DigiFennek/TransputerBox/MCUXpresso/transputerBox_WinUSB_cm4/source/libusbdev_desc.c

/*
 * @brief USB Band Width and WCID example descriptors.
 *
 * @note
 * Copyright(C) NXP Semiconductors, 2013
 * All rights reserved.
 *
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
 * @par
 * Permission to use, copy, modify, and distribute this software and its
 * documentation is hereby granted, under NXP Semiconductors' and its
 * licensor's relevant copyrights in the software, without fee, provided that it
 * is used in conjunction with NXP Semiconductors microcontrollers.  This
 * copyright, permission, and disclaimer notice must appear in all copies of
 * this code.
 */

#include "app_usbd_cfg.h"
#include "usbd_rom_api.h"

/*****************************************************************************
 * Private types/enumerations/variables
 ****************************************************************************/

/*****************************************************************************
 * Public types/enumerations/variables
 ****************************************************************************/

/**
 * USB Standard Device Descriptor
 */
ALIGN(4) const uint8_t USB_DeviceDescriptor[] = {
	USB_DEVICE_DESC_SIZE,				/* bLength */
	USB_DEVICE_DESCRIPTOR_TYPE,			/* bDescriptorType */
	WBVAL(0x0200),						/* bcdUSB: 2.00 */
	0x00,								/* bDeviceClass */
	0x00,								/* bDeviceSubClass */
	0x00,								/* bDeviceProtocol */
	USB_MAX_PACKET0,					/* bMaxPacketSize0 */
	WBVAL(0x1FC9),						/* idVendor */
	WBVAL(LUSB_PID),					/* idProduct */
	WBVAL(0x0100),						/* bcdDevice: 1.00 */
	0x01,								/* iManufacturer */
	0x02,								/* iProduct */
	0x03,								/* iSerialNumber */
	0x01								/* bNumConfigurations */
};

/**
 * USB FSConfiguration Descriptor
 * All Descriptors (Configuration, Interface, Endpoint, Class, Vendor)
 */
ALIGNED(4) uint8_t USB_FsConfigDescriptor[] = {
	/* Configuration 1 */
	USB_CONFIGURATION_DESC_SIZE,		/* bLength */
	USB_CONFIGURATION_DESCRIPTOR_TYPE,	/* bDescriptorType */
	WBVAL(							/* wTotalLength */
		USB_CONFIGURATION_DESC_SIZE +
		USB_INTERFACE_DESC_SIZE     +
		LUSB_NUM_OF_EP * USB_ENDPOINT_DESC_SIZE
		),
	0x01,							/* bNumInterfaces */
	0x01,							/* bConfigurationValue */
	0x00,							/* iConfiguration */
	USB_CONFIG_SELF_POWERED,		/* bmAttributes */
	USB_CONFIG_POWER_MA(100),		/* bMaxPower */
	/* Interface 0, Alternate Setting 0, Custom Class */
	USB_INTERFACE_DESC_SIZE,		/* bLength */
	USB_INTERFACE_DESCRIPTOR_TYPE,	/* bDescriptorType */
	0x00,							/* bInterfaceNumber */
	0x00,							/* bAlternateSetting */
	LUSB_NUM_OF_EP,					/* bNumEndpoints */
	0xFF,							/* bInterfaceClass */
	0xF0,							/* bInterfaceSubClass */
	0x00,							/* bInterfaceProtocol */
	0x04,							/* iInterface */
	/* Bulk Out Endpoint */
	USB_ENDPOINT_DESC_SIZE,			/* bLength */
	USB_ENDPOINT_DESCRIPTOR_TYPE,	/* bDescriptorType */
	LUSB_OUT_EP,					/* bEndpointAddress */
	USB_ENDPOINT_TYPE_BULK,			/* bmAttributes */
	WBVAL(USB_FS_MAX_BULK_PACKET),	/* wMaxPacketSize */
	0,								/* bInterval */
	/* Bulk In Endpoint */
	USB_ENDPOINT_DESC_SIZE,			/* bLength */
	USB_ENDPOINT_DESCRIPTOR_TYPE,	/* bDescriptorType */
	LUSB_IN_EP,						/* bEndpointAddress */
	USB_ENDPOINT_TYPE_BULK,			/* bmAttributes */
	WBVAL(USB_FS_MAX_BULK_PACKET),	/* wMaxPacketSize */
	0,								/* bInterval */
	/* INT Out Endpoint */
	USB_ENDPOINT_DESC_SIZE,			/* bLength */
	USB_ENDPOINT_DESCRIPTOR_TYPE,	/* bDescriptorType */
	LUSB_INTR_OUT_EP,				/* bEndpointAddress */
	USB_ENDPOINT_TYPE_INTERRUPT,	/* bmAttributes */
	WBVAL(sizeof(uint32_t)),        /* wMaxPacketSize */
	0,	     						/* bInterval: 8 ms */
	/* INT In Endpoint */
	USB_ENDPOINT_DESC_SIZE,			/* bLength */
	USB_ENDPOINT_DESCRIPTOR_TYPE,	/* bDescriptorType */
	LUSB_INTR_IN_EP,				/* bEndpointAddress */
	USB_ENDPOINT_TYPE_INTERRUPT,	/* bmAttributes */
	WBVAL(sizeof(uint32_t)),		/* wMaxPacketSize */
	0x8,							/* bInterval: 8 ms */
	/* Terminator */
	0								/* bLength */
};

/**
 * USB String Descriptor (optional)
 */
const uint8_t USB_StringDescriptor[] = {
	/* Index 0x00: LANGID Codes */
	0x04,							/* bLength */
	USB_STRING_DESCRIPTOR_TYPE,		/* bDescriptorType */
	WBVAL(0x0409),					/* wLANGID  0x0409 = US English*/
	/* Index 0x01: Manufacturer */
	(10 * 2 + 2),					/* bLength (18 Char + Type + length) */
	USB_STRING_DESCRIPTOR_TYPE,		/* bDescriptorType */
	'D', 0,
	'i', 0,
	'g', 0,
	'i', 0,
	'F', 0,
	'e', 0,
	'n', 0,
	'n', 0,
	'e', 0,
	'k', 0,
	/* Index 0x02: Product */
	(27 * 2 + 2),					/* bLength (15 Char + Type + length) */
	USB_STRING_DESCRIPTOR_TYPE,		/* bDescriptorType */
	'T', 0,
	'r', 0,
	'a', 0,
	'n', 0,
	's', 0,
	'p', 0,
	'u', 0,
	't', 0,
	'e', 0,
	'r', 0,
	'B', 0,
	'o', 0,
	'x', 0,
	' ', 0,
	'U', 0,
	'S', 0,
	'B', 0,
	' ', 0,
	'I', 0,
	'n', 0,
	't', 0,
	'e', 0,
	'r', 0,
	'f', 0,
	'a', 0,
	'c', 0,
	'e', 0,
	/* Index 0x03: Serial Number */
	(13 * 2 + 2),					/* bLength (13 Char + Type + length) */
	USB_STRING_DESCRIPTOR_TYPE,		/* bDescriptorType */
	'A', 0,
	'B', 0,
	'C', 0,
	'D', 0,
	'1', 0,
	'2', 0,
	'3', 0,
	'4', 0,
	'5', 0,
	'6', 0,
	'7', 0,
	'8', 0,
	'9', 0,
	/* Index 0x04: Interface 0, Alternate Setting 0 */
	(6 * 2 + 2),					/* bLength (6 Char + Type + length) */
	USB_STRING_DESCRIPTOR_TYPE,		/* bDescriptorType */
	'S', 0,
	't', 0,
	'r', 0,
	'e', 0,
	'a', 0,
	'm', 0,
};

/* WCID USB: Microsoft String Descriptor */
ALIGNED(4) const uint8_t WCID_String_Descriptor[] = {
	(8 * 2 + 2),					/* bLength (8 Char + Type + length) */
	USB_STRING_DESCRIPTOR_TYPE,		/* bDescriptorType */
	'M', 0,
	'S', 0,
	'F', 0,
	'T', 0,
	'1', 0,
	'0', 0,
	'0', 0,
	LUSB_PID, 0,
};

/* WCID USB: Microsoft Compatible ID Feature Descriptor */
ALIGNED(4) const uint8_t WCID_CompatID_Descriptor[] = {
	0x28, 0x00, 0x00, 0x00,						/* Length 40 bytes */
	0x00, 0x01,									/* Version */
	0x04, 0x00,									/* Compatibility ID Descriptor index  */
	0x01,										/* Number of sections */
	0x00, 0x00, 0x00, 0x00,
	0x00, 0x00, 0x00,							/* Reserved: 7 bytes */
	0x00,										/* Interface Number */
	0x01,										/* Reserved */
	'W', 'I', 'N', 'U', 'S', 'B', 0x00, 0x00,	/* Compatible ID: 8 bytes ASCII */
	0x00, 0x00, 0x00, 0x00,
	0x00, 0x00, 0x00, 0x00,						/* Sub-Compatible ID: 8 bytes ASCII*/
	0x00, 0x00, 0x00, 0x00,
	0x00, 0x00,									/* Reserved: 6 bytes */
};

/* WCID USB: Microsoft Extended Properties Feature Descriptor */
/* https://github.com/pbatard/libwdi/wiki/WCID-Devices#What_is_WCID */
ALIGNED(4) const uint8_t WCID_Properties_Descriptor[] = {
    0x8E, 0x00, 0x00, 0x00, 					/* Length 142 Bytes */
    0x00, 0x01,            						/* Version */
    0x05, 0x00,  	   							/* Descriptor index */
    0x01, 0x00,            						/* Number of sections */
    0x84, 0x00, 0x00, 0x00, 					/* Size of the property section (132 bytes) */
    0x01, 0x00, 0x00, 0x00,						/* Property data type */
    0x28, 0x00,    	   							/* Property name length (40 bytes) */
    'D', 0,
    'e', 0,
    'v', 0,
    'i', 0,
    'c', 0,
    'e', 0,
    'I', 0,
    'n', 0,
    't', 0,
    'e', 0,
    'r', 0,
    'f', 0,
    'a', 0,
    'c', 0,
    'e', 0,
    'G', 0,
    'U', 0,
    'I', 0,
    'D', 0,
    0x00, 0x00,            						/* NUL-terminated */
    0x4e, 0x00, 0x00, 0x00, 					/* Property data length (78 bytes) {60833b09-7fde-4410-afd1-541efdf36d8a} */
    '{', 0,
    '6', 0,
    '0', 0,
    '8', 0,
    '3', 0,
    '3', 0,
    'b', 0,
    '0', 0,
    '9', 0,
    '-', 0,
    '7', 0,
    'f', 0,
    'd', 0,
    'e', 0,
    '-', 0,
    '4', 0,
    '4', 0,
    '1', 0,
    '0', 0,
    '-', 0,
    'a', 0,
    'f', 0,
    'd', 0,
    '1', 0,
    '-', 0,
    '5', 0,
    '4', 0,
    '1', 0,
    'e', 0,
    'f', 0,
    'd', 0,
    'f', 0,
    '3', 0,
    '6', 0,
    'd', 0,
    '8', 0,
    'a', 0,
    '}', 0,
    0x00, 0x00,            						/* NUL-terminated */
};
