DigiFennek/TransputerBox/MCUXpresso/transputerBox_WinUSB_cm4/source/inc/lpc_types.h

/*
 * @brief Common types used in LPC functions
 *
 * @note
 * Copyright  2012, NXP
 * All rights reserved.
 *
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
 * @par
 * Permission to use, copy, modify, and distribute this software and its
 * documentation is hereby granted, under NXP Semiconductors' and its
 * licensor's relevant copyrights in the software, without fee, provided that it
 * is used in conjunction with NXP Semiconductors microcontrollers.  This
 * copyright, permission, and disclaimer notice must appear in all copies of
 * this code.
 */

#ifndef __LPC_TYPES_H_
#define __LPC_TYPES_H_

#include <stdint.h>
#include <stdbool.h>

/** @defgroup LPC_Types CHIP: LPC Common Types
 * @ingroup CHIP_Common
 * @{
 */

/** @defgroup LPC_Types_Public_Types LPC Public Types
 * @{
 */

/**
 * @brief Boolean Type definition
 */
typedef enum
{
    FALSE = 0,
    TRUE  = !FALSE
} Bool;

/**
 * @brief Boolean Type definition
 */
#if !defined(__cplusplus)
// typedef enum {false = 0, true = !false} bool;
#endif

/**
 * @brief Flag Status and Interrupt Flag Status type definition
 */
typedef enum
{
    RESET = 0,
    SET   = !RESET
} FlagStatus,
    IntStatus, SetState;
#define PARAM_SETSTATE(State) ((State == RESET) || (State == SET))

/**
 * @brief Functional State Definition
 */
typedef enum
{
    DISABLE = 0,
    ENABLE  = !DISABLE
} FunctionalState;
#define PARAM_FUNCTIONALSTATE(State) ((State == DISABLE) || (State == ENABLE))

/**
 * @ Status type definition
 */
typedef enum
{
    ERROR   = 0,
    SUCCESS = !ERROR
} Status;

/**
 * Read/Write transfer type mode (Block or non-block)
 */
typedef enum
{
    NONE_BLOCKING = 0, /**< None Blocking type */
    BLOCKING,          /**< Blocking type */
} TRANSFER_BLOCK_T;

/** Pointer to Function returning Void (any number of parameters) */
typedef void (*PFV)();

/** Pointer to Function returning int32_t (any number of parameters) */
typedef int32_t (*PFI)();

/**
 * @}
 */

/** @defgroup LPC_Types_Public_Macros  LPC Public Macros
 * @{
 */

/* _BIT(n) sets the bit at position "n"
 * _BIT(n) is intended to be used in "OR" and "AND" expressions:
 * e.g., "(_BIT(3) | _BIT(7))".
 */
#undef _BIT
/* Set bit macro */
#define _BIT(n) (1 << (n))

/* _SBF(f,v) sets the bit field starting at position "f" to value "v".
 * _SBF(f,v) is intended to be used in "OR" and "AND" expressions:
 * e.g., "((_SBF(5,7) | _SBF(12,0xF)) & 0xFFFF)"
 */
#undef _SBF
/* Set bit field macro */
#define _SBF(f, v) ((v) << (f))

/* _BITMASK constructs a symbol with 'field_width' least significant
 * bits set.
 * e.g., _BITMASK(5) constructs '0x1F', _BITMASK(16) == 0xFFFF
 * The symbol is intended to be used to limit the bit field width
 * thusly:
 * <a_register> = (any_expression) & _BITMASK(x), where 0 < x <= 32.
 * If "any_expression" results in a value that is larger than can be
 * contained in 'x' bits, the bits above 'x - 1' are masked off.  When
 * used with the _SBF example above, the example would be written:
 * a_reg = ((_SBF(5,7) | _SBF(12,0xF)) & _BITMASK(16))
 * This ensures that the value written to a_reg is no wider than
 * 16 bits, and makes the code easier to read and understand.
 */
#undef _BITMASK
/* Bitmask creation macro */
#define _BITMASK(field_width) (_BIT(field_width) - 1)

/* NULL pointer */
#ifndef NULL
#define NULL ((void *)0)
#endif

/* Number of elements in an array */
#define NELEMENTS(array) (sizeof(array) / sizeof(array[0]))

/* Static data/function define */
#define STATIC static
/* External data/function define */
#define EXTERN extern

#if !defined(MAX)
#define MAX(a, b) (((a) > (b)) ? (a) : (b))
#endif
#if !defined(MIN)
#define MIN(a, b) (((a) < (b)) ? (a) : (b))
#endif

/**
 * @}
 */

/* Old Type Definition compatibility */
/** @addtogroup LPC_Types_Public_Types
 * @{
 */

/** LPC type for character type */
typedef char CHAR;

/** LPC type for 8 bit unsigned value */
typedef uint8_t UNS_8;

/** LPC type for 8 bit signed value */
typedef int8_t INT_8;

/** LPC type for 16 bit unsigned value */
typedef uint16_t UNS_16;

/** LPC type for 16 bit signed value */
typedef int16_t INT_16;

/** LPC type for 32 bit unsigned value */
typedef uint32_t UNS_32;

/** LPC type for 32 bit signed value */
typedef int32_t INT_32;

/** LPC type for 64 bit signed value */
typedef int64_t INT_64;

/** LPC type for 64 bit unsigned value */
typedef uint64_t UNS_64;

#ifdef __CODE_RED
#define BOOL_32 bool
#define BOOL_16 bool
#define BOOL_8 bool
#else
/** 32 bit boolean type */
typedef bool BOOL_32;

/** 16 bit boolean type */
typedef bool BOOL_16;

/** 8 bit boolean type */
typedef bool BOOL_8;
#endif

#if defined(__CC_ARM) || (defined(__ARMCC_VERSION))
#define INLINE __inline
#else
#define INLINE inline
#endif

#ifdef __ICCARM__
#define ALIGNSTR(x) #x
#define ALIGN(x) _Pragma(ALIGNSTR(data_alignment = x))
#define WEAK __weak
#else /* __CC_ARM || __ARMCC_VERSION || __GNUC__ */
#define ALIGN(x) __attribute__((aligned(x)))
#define WEAK __attribute__((weak))
#endif

/**
 * @}
 */

/**
 * @}
 */

#endif /* __LPC_TYPES_H_ */
